maynej/Smarthome-1x1-Module/Imatges/TapaCPU_LCD_Touch.png

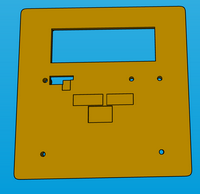
Imatges/TapaCPU_LCD_Touch.png
