maynej/Smarthome-1x1-Module/STL/Finestres/VidrieraGran.stl

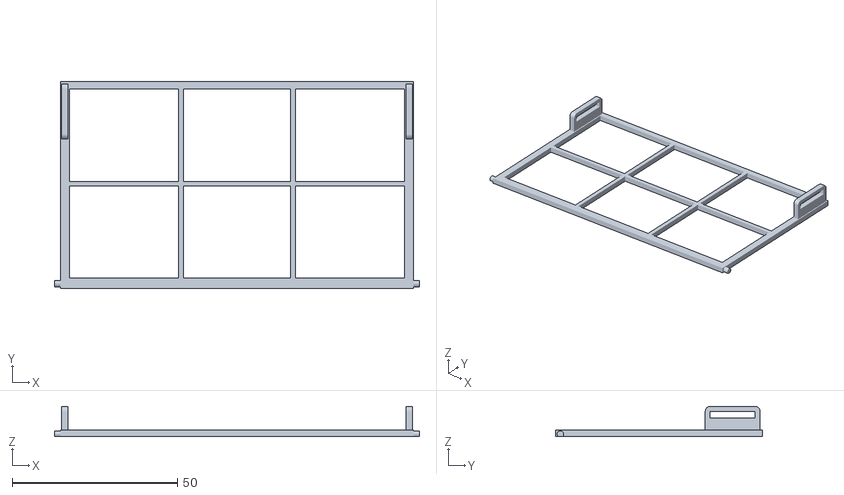
[picture p86: CAD file, 2022-06-26]
STL/Finestres/VidrieraGran.stl
110.6 x 62.8 x 9.18
