maynej/Smarthome-1x1-Module/STL/Parets/ParetH1.stl

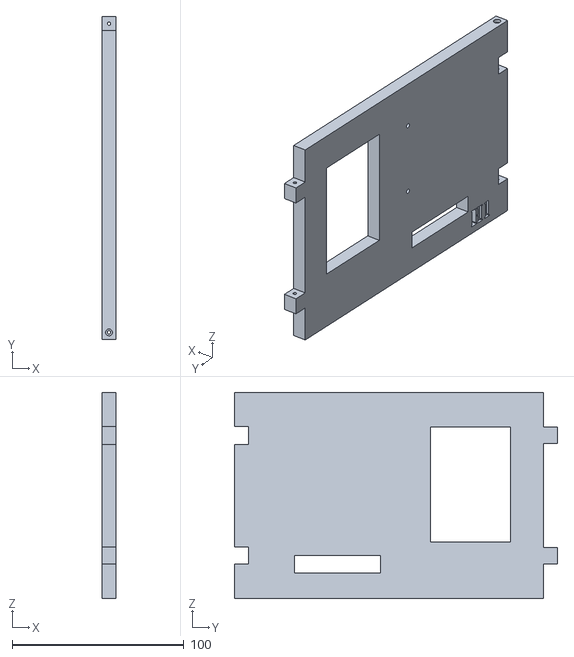
[picture p87: CAD file, 2022-07-13]
STL/Parets/ParetH1.stl
8.00 x 188.0 x 120.0
