maynej/Smarthome-1x1-Module/STL/Parets/ParetsSolidesOpcionals/ParetBase_Femella_Femella.stl

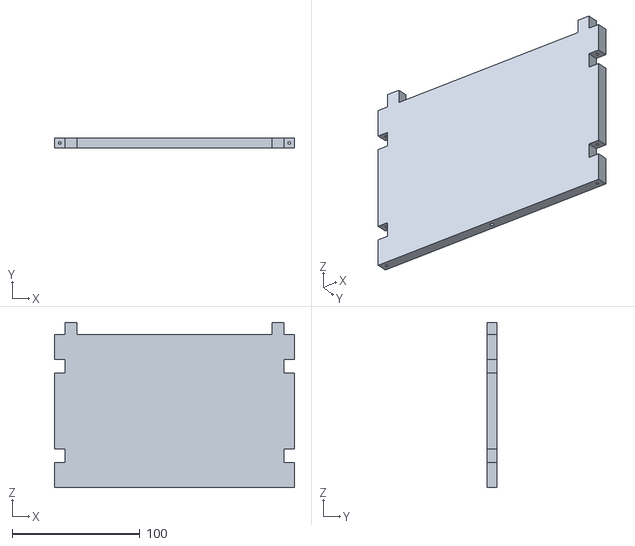
[picture p88: CAD file, 2022-07-13]
STL/Parets/ParetsSolidesOpcionals/ParetBase_Femella_Femella.stl
188.0 x 8.00 x 129.5
