maynej/Smarthome-1x1-Module/STL/Porta/MarcPorta.stl

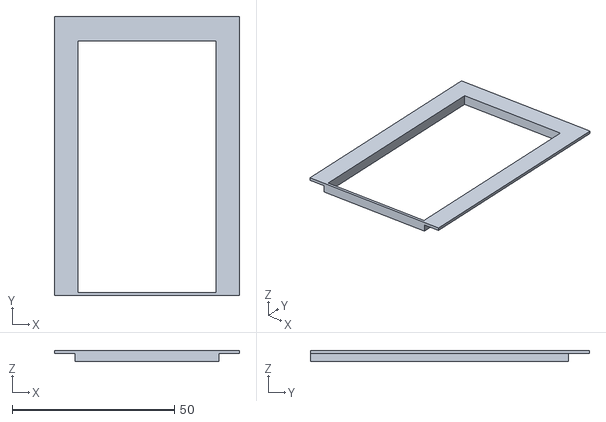
[picture p89: CAD file, 2022-06-26]
STL/Porta/MarcPorta.stl
57.0 x 86.0 x 3.50
