maynej/Smarthome-1x1-Module/STL/SuportsModuls/Suport1forat/Suport1forat_2.stl

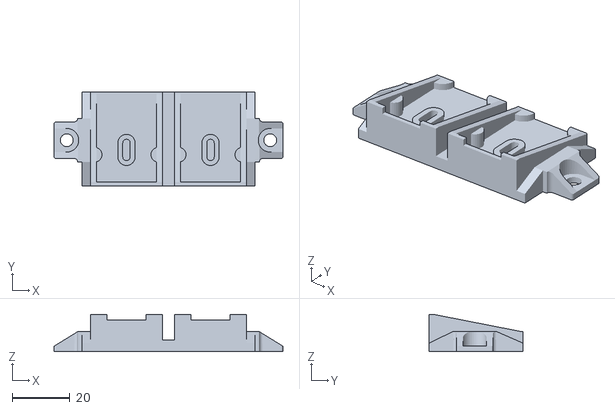
[picture p90: CAD file, 2022-07-21]
STL/SuportsModuls/Suport1forat/Suport1forat_2.stl
79.6 x 32.6 x 13.0
