maynej/Smarthome-1x1-Module/STL/SuportsModuls/Suport2forats/Suport2forats_2.stl

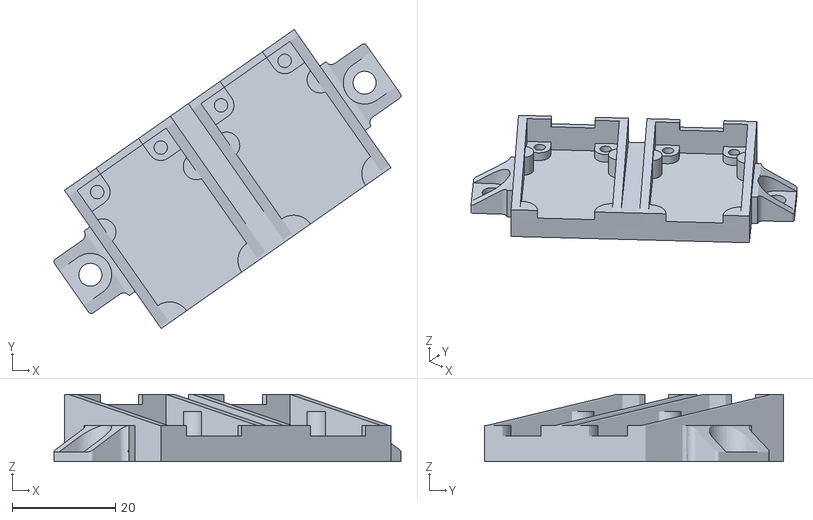
[picture p91: CAD file, 2022-07-21]
STL/SuportsModuls/Suport2forats/Suport2forats_2.stl
67.1 x 57.8 x 13.0
