maynej/Smarthome-1x1-Module/STL/SuportsModuls/SuportInclinat1forat/SuportInclinat1forat_2.stl

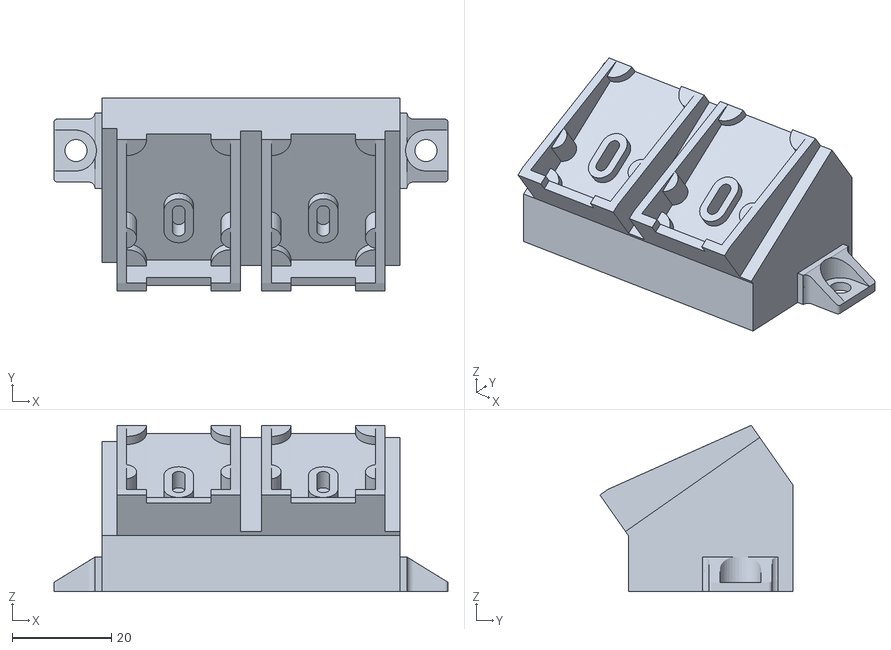
[picture p92: CAD file, 2022-07-21]
STL/SuportsModuls/SuportInclinat1forat/SuportInclinat1forat_2.stl
79.6 x 39.0 x 33.6
