maynej/Smarthome-1x1-Module/STL/Teulada/TeuladaPartida2.stl

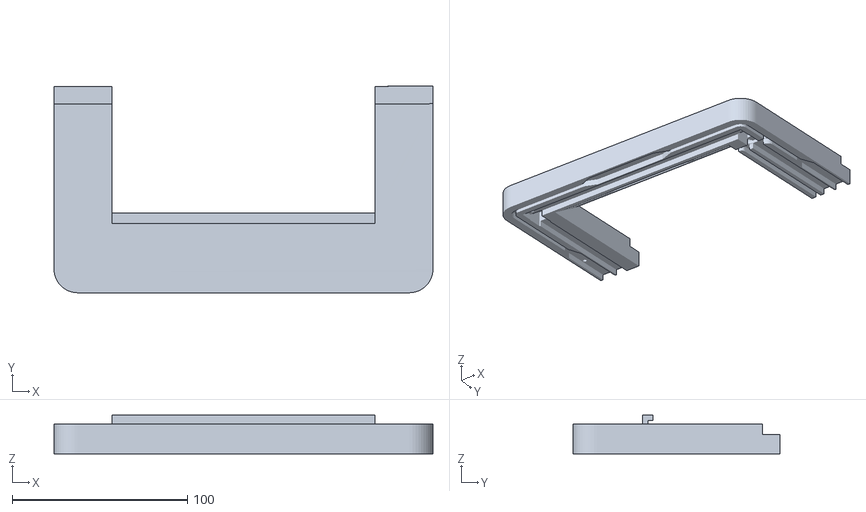
[picture p93: CAD file, 2022-07-05]
STL/Teulada/TeuladaPartida2.stl
216.0 x 117.7 x 22.0
