maynej/Smarthome-1x1-Module/STL/Finestres/MarcFinestraPetita.stl

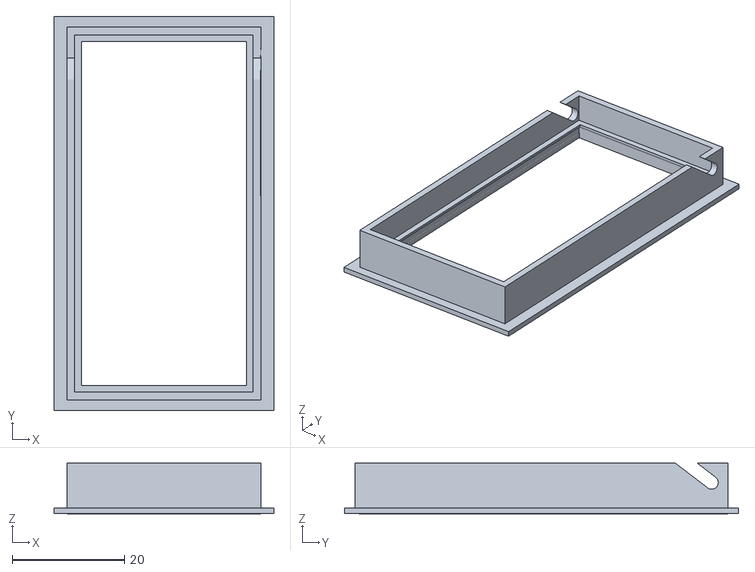
[picture p94: CAD file, 2022-06-26]
STL/Finestres/MarcFinestraPetita.stl
39.2 x 70.3 x 9.06
