maynej/Smarthome-1x1-Module/STL/Parets/ParetC1.stl

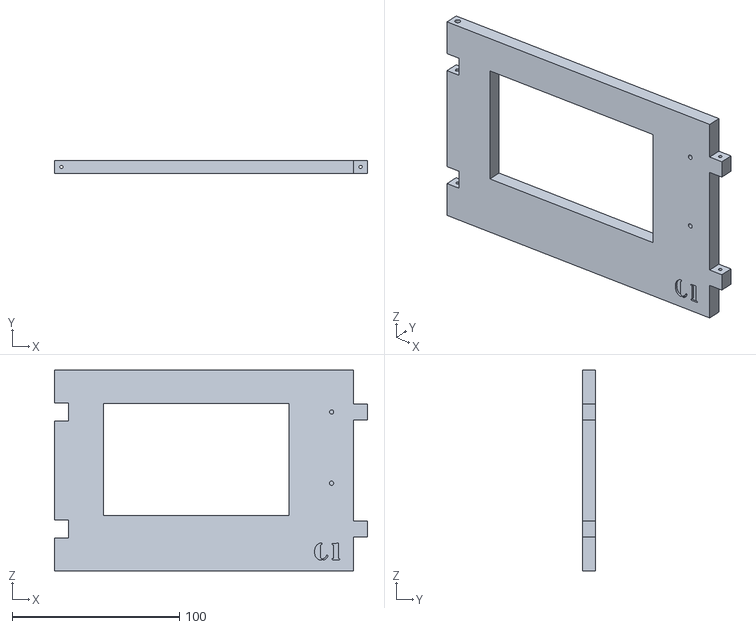
[picture p95: CAD file, 2022-06-26]
STL/Parets/ParetC1.stl
187.2 x 8.05 x 120.0
