maynej/Smarthome-1x1-Module/STL/Porta/PomPorta.stl

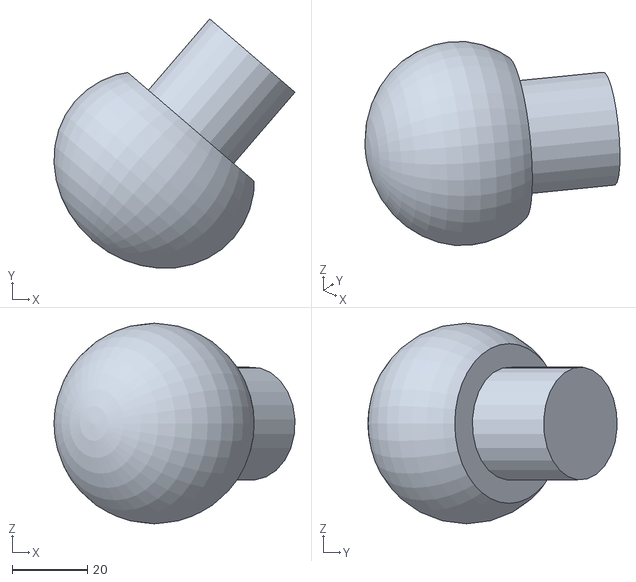
[picture p96: CAD file, 2022-06-26]
STL/Porta/PomPorta.stl
64.1 x 66.3 x 53.3
