maynej/Smarthome-1x1-Module/STL/SuportsModuls/Suport1forat/Suport1forat_3.stl

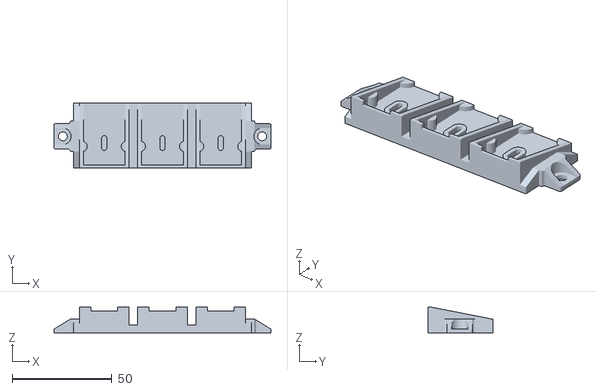
[picture p97: CAD file, 2022-07-13]
STL/SuportsModuls/Suport1forat/Suport1forat_3.stl
108.8 x 32.6 x 13.0
