maynej/Smarthome-1x1-Module/STL/SuportsModuls/Suport2forats/Suport2forats_3.stl

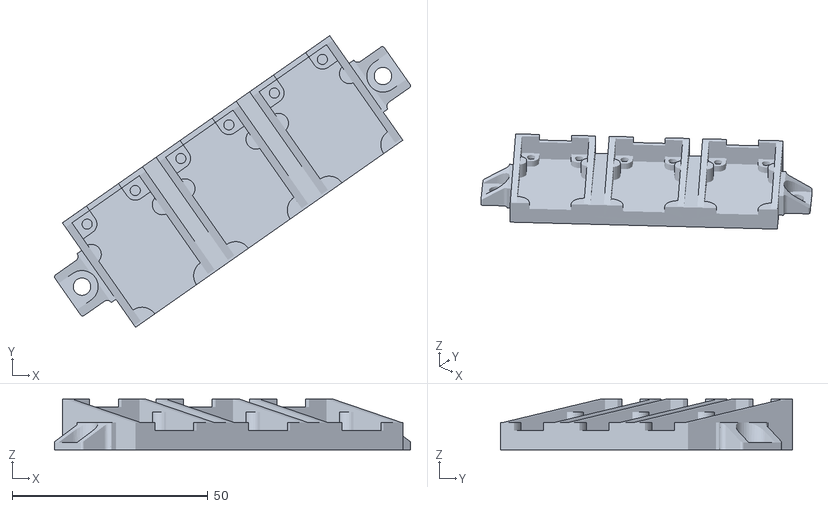
[picture p98: CAD file, 2022-06-28]
STL/SuportsModuls/Suport2forats/Suport2forats_3.stl
91.0 x 74.5 x 13.0
