maynej/Smarthome-1x1-Module/STL/SuportsModuls/SuportInclinat1forat/SuportInclinat1forat_3.stl

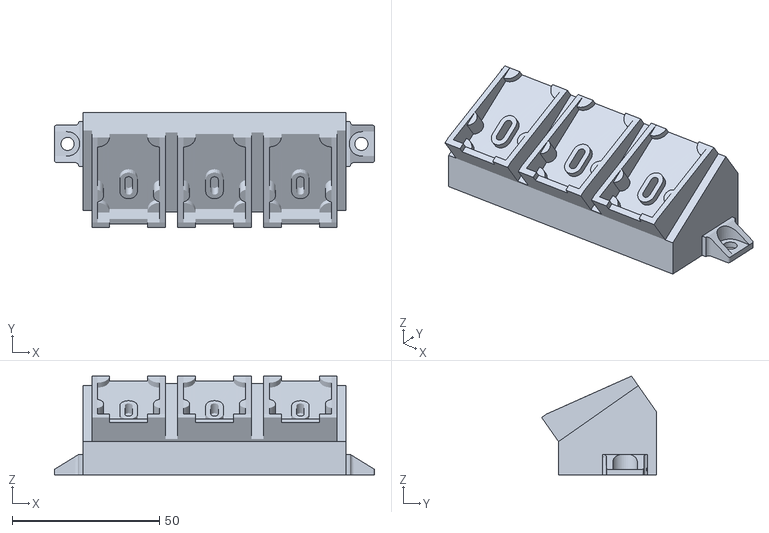
[picture p99: CAD file, 2022-06-26]
STL/SuportsModuls/SuportInclinat1forat/SuportInclinat1forat_3.stl
108.8 x 39.0 x 33.6
