maynej/Smarthome-1x1-Module/STL/Finestres/VidrieraPetita.stl

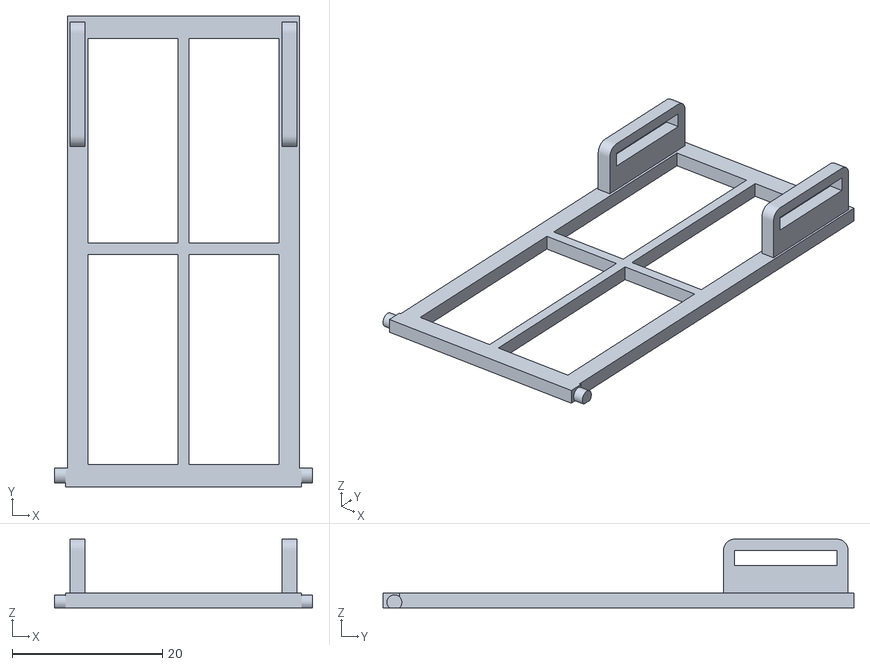
[picture p100: CAD file, 2022-06-26]
STL/Finestres/VidrieraPetita.stl
34.4 x 62.8 x 9.18
