maynej/Smarthome-1x1-Module/STL/Parets/ParetA1.stl

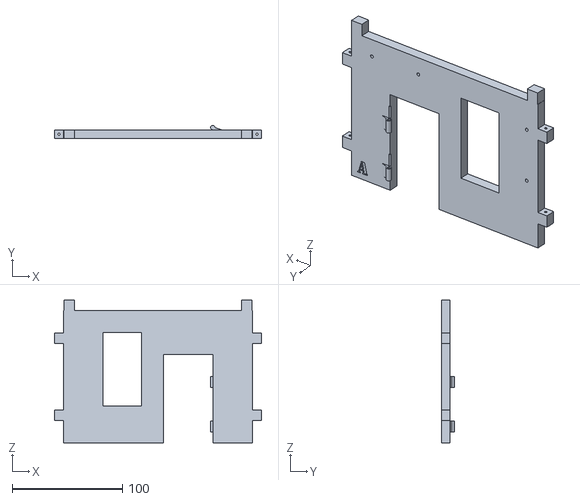
[picture p101: CAD file, 2022-06-26]
STL/Parets/ParetA1.stl
188.0 x 12.0 x 129.5
