maynej/Smarthome-1x1-Module/STL/Finestres/MarcFinestraGran.stl

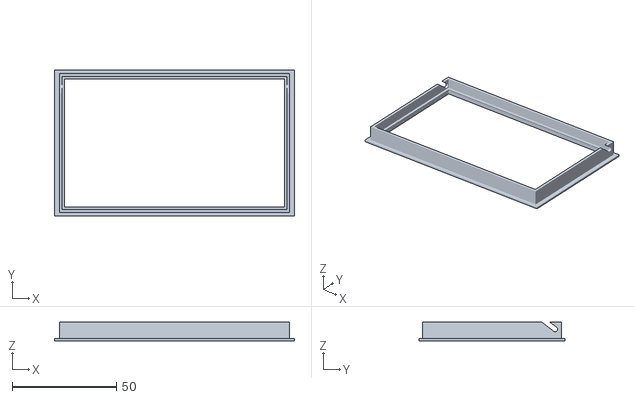
[picture p102: CAD file, 2022-06-26]
STL/Finestres/MarcFinestraGran.stl
115.2 x 70.3 x 9.06
