maynej/Smarthome-1x1-Module/STL/Parets/ParetT1.stl

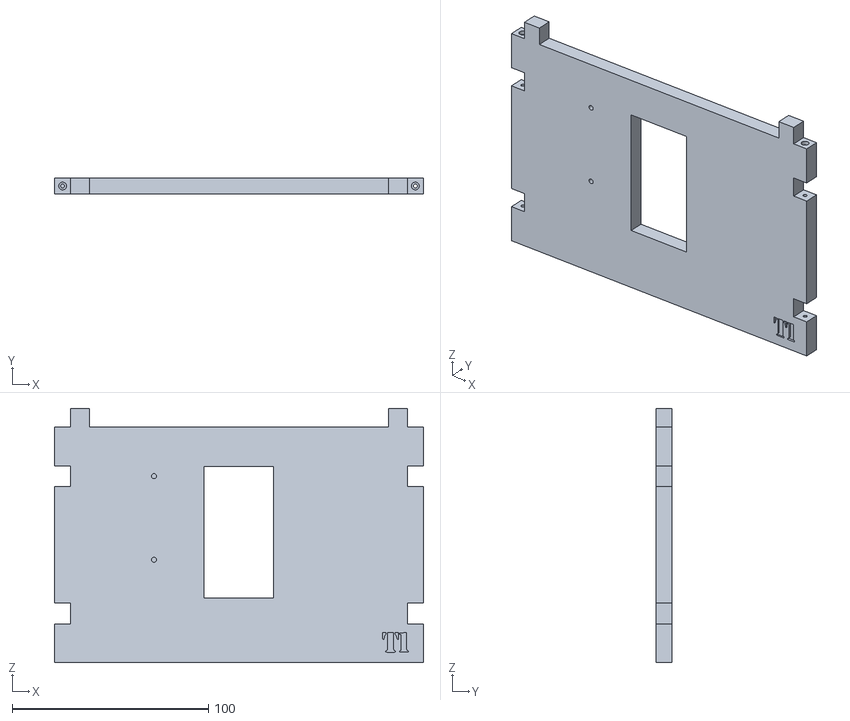
[picture p103: CAD file, 2022-06-26]
STL/Parets/ParetT1.stl
188.0 x 8.00 x 129.5
