maynej/Smarthome-1x1-Module/STL/Finestres/MarcFinestraMitjana.stl

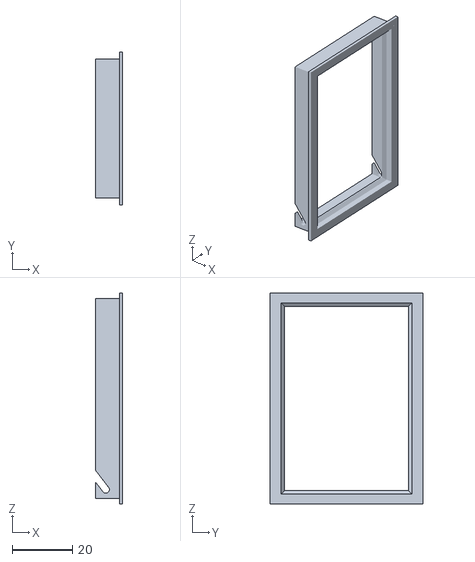
[picture p104: CAD file, 2022-06-26]
STL/Finestres/MarcFinestraMitjana.stl
9.06 x 51.0 x 70.3
